floktl/Self-Driving-Car-model/Documentation/car_github_schematic.kicad_sch

## KiCad design Documentation/car_github_schematic.kicad_sch (2025-02-14)

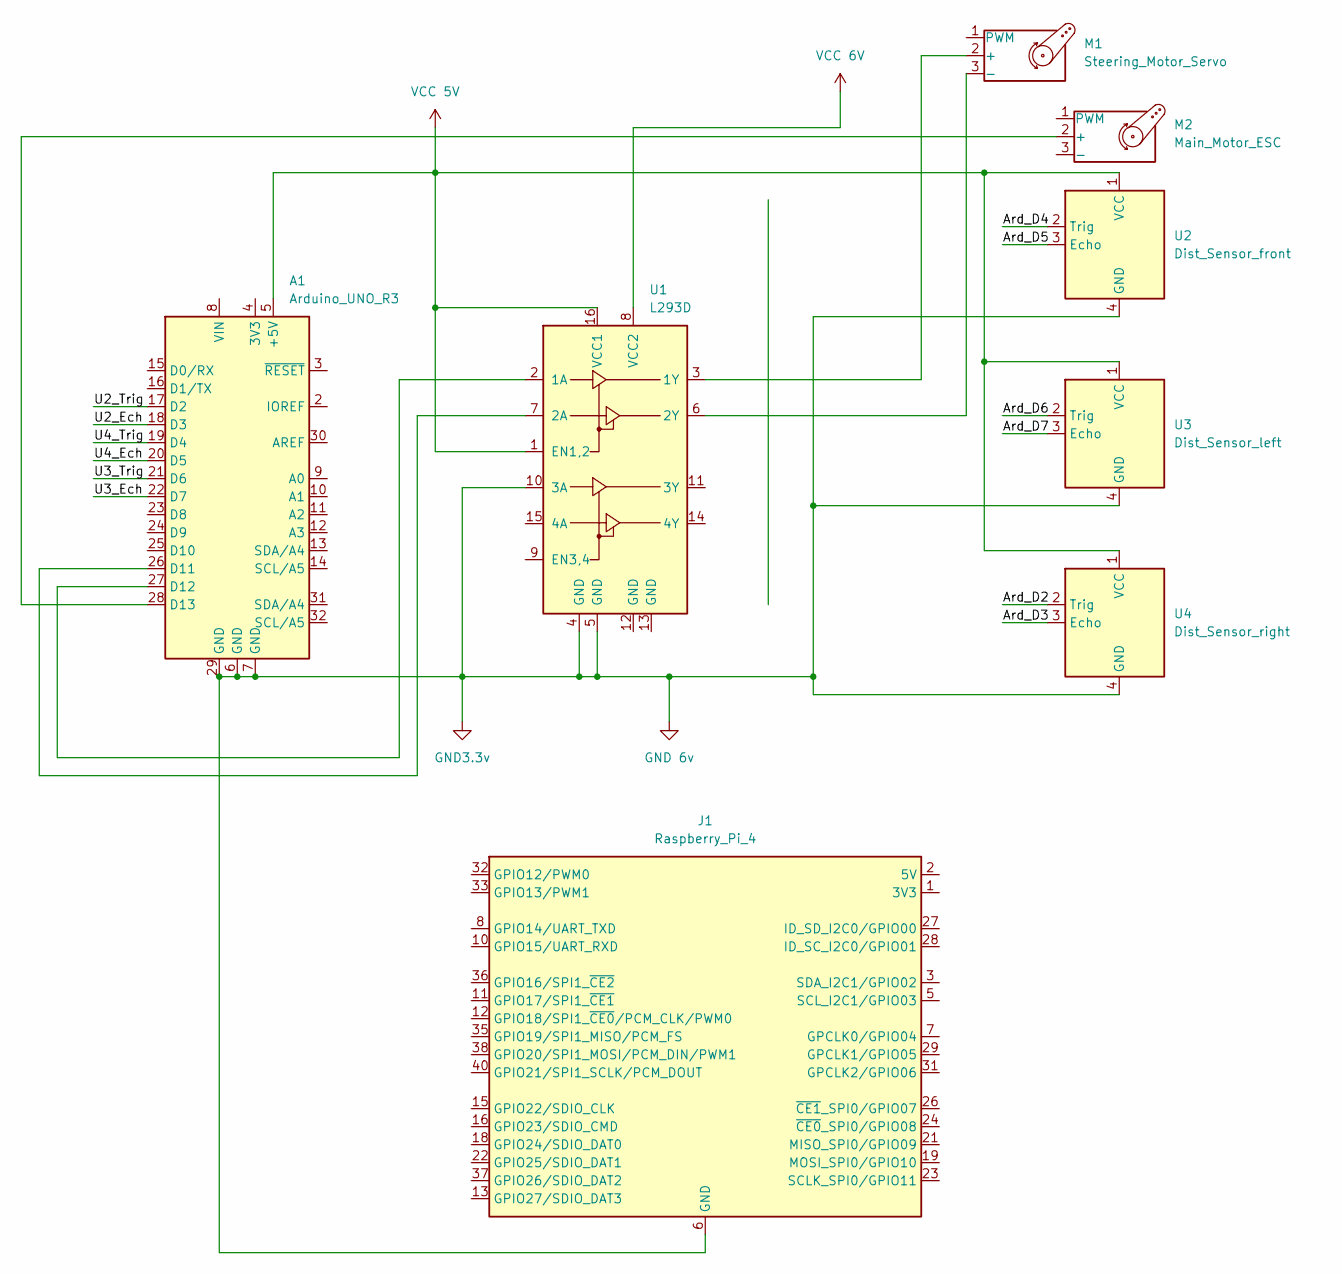
[picture p4: schematic car_github_schematic.kicad_sch]

Parts:
A1: Arduino_UNO_R3
J1: Raspberry_Pi_4
M1: Steering_Motor_Servo
M2: Main_Motor_ESC
U1: L293D; DIP-16_W7.62mm
U2: Dist_Sensor_front; HCSR04
U3: Dist_Sensor_left; HCSR04
U4: Dist_Sensor_right; HCSR04

Connections:
Ard_D2: U4.2 (Trig)
Ard_D3: U4.3 (Echo)
Ard_D4: U2.2 (Trig)
Ard_D5: U2.3 (Echo)
Ard_D6: U3.2 (Trig)
Ard_D7: U3.3 (Echo)
GND 6v: A1.6 (GND), A1.7 (GND), A1.29 (GND), J1.6 (GND), J1.9 (GND), J1.14 (GND), J1.20 (GND), J1.25 (GND), J1.30 (GND), J1.34 (GND), J1.39 (GND), U1.4 (GND), U1.5 (GND), U1.10 (3A), U2.4 (GND), U3.4 (GND), U4.4 (GND)
unnamed: A1.26 (D11), U1.7 (2A)
unnamed: A1.27 (D12), U1.2 (1A)
unnamed: A1.28 (D13), M2.2 (+)
unnamed: J1.1 (3V3), J1.17 (3V3)
unnamed: J1.2 (5V), J1.4 (5V)
unnamed: M1.2 (+), U1.3 (1Y)
unnamed: M1.3 (-), U1.6 (2Y)
unnamed: U2.4 (GND), U2.8 (GND)
unnamed: U3.4 (GND), U3.8 (GND)
unnamed: U4.4 (GND), U4.8 (GND)
U2_Ech: A1.18 (D3)
U2_Trig: A1.17 (D2)
U3_Ech: A1.22 (D7)
U3_Trig: A1.21 (D6)
U4_Ech: A1.20 (D5)
U4_Trig: A1.19 (D4)
VCC 5V: A1.5 (+5V), U1.1 (EN1,2), U1.16 (VCC1), U2.1 (VCC), U2.7 (VDD), U2.12 (VDD), U3.1 (VCC), U3.7 (VDD), U3.12 (VDD), U4.1 (VCC), U4.7 (VDD), U4.12 (VDD)
VCC 6V: U1.8 (VCC2)
